Tinkerforge/wifi-v2-extension/software/src/configuration.c

/* WIFI Extension 2.0
 * Copyright (C) 2015 Olaf Lüke <olaf@tinkerforge.com>
 * Copyright (C) 2016 Ishraq Ibne Ashraf <ishraq@tinkerforge.com>
 * Copyright (C) 2020 Matthias Bolte <matthias@tinkerforge.com>
 *
 * configuration.c: WIFI Extension configuration handling
 *
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
 * You should have received a copy of the GNU Lesser General Public
 * License along with this library; if not, write to the
 * Free Software Foundation, Inc., 59 Temple Place - Suite 330,
 * Boston, MA 02111-1307, USA.
 */

#define _GNU_SOURCE // for strnlen
#undef __STRICT_ANSI__ // for strnlen

#include <string.h> // for strnlen

#include "configuration.h"
#include "espmissingincludes.h"
#include "eeprom.h"
#include "ip_addr.h"
#include "espconn.h"
#include "osapi.h"
#include "user_interface.h"
#include "pearson_hash.h"
#include "communication.h"
#include "logging.h"
#include "mesh.h"
#include "tfp_mesh_connection.h"
#include "tfp_connection.h"

extern os_timer_t tmr_tfp_mesh_enable;

const Configuration configuration_default = {
	// Configuration info
	.conf_checksum = 0,
	.conf_version = CONFIGURATION_EXPECTED_VERSION,
	.conf_length = sizeof(Configuration),

	// General configuration
	.general_port = 4223,
	.general_websocket_port = 4280,
	.general_website_port = 80,
	.general_phy_mode = 1,
	.general_sleep_mode = 0, // Currently unused
	.general_website = 1,
	.general_authentication_secret = "",

	// Client configuration
	.client_enable = 1,
	.client_ssid = "Your Access Point",
	.client_ip = {0, 0, 0, 0},
	.client_subnet_mask = {0, 0, 0, 0},
	.client_gateway = {0, 0, 0, 0},
	.client_mac_address = {0, 0, 0, 0, 0, 0},
	.client_bssid = {0, 0, 0, 0, 0, 0},
	.client_hostname = "wifi-extension-v2",
	.client_password = "password",

	// AP configuration
	.ap_enable = 1,
	.ap_ssid = "WIFI Extension 2.0 Access Point",
	.ap_ip = {0, 0, 0, 0},
	.ap_subnet_mask = {0, 0, 0, 0},
	.ap_gateway = {0, 0, 0, 0},
	.ap_encryption = 4,
	.ap_hidden = false,
	.ap_mac_address = {0, 0, 0, 0, 0, 0},
	.ap_channel = 1,
	.ap_hostname = "\0", // Currently unused
	.ap_password = "password",

	// Mesh configuration
	.mesh_enable = 0,
	.mesh_router_ssid = "Your Access Point",
	.mesh_router_password = "password",
	.mesh_root_ip = {0, 0, 0, 0},
	.mesh_root_subnet_mask = {0, 0, 0, 0},
	.mesh_root_gateway = {0, 0, 0, 0},
	.mesh_router_bssid = {0, 0, 0, 0, 0, 0}, // Must be set if mesh router is hidden.
	.mesh_group_ssid_prefix = "TF_MESH",
	.mesh_password = "password",
	.mesh_group_id = {0x1A, 0xFE, 0x34, 0x00, 0x00, 0x00},
	.mesh_gateway_hostname = "\0", // Currently unused.
	.mesh_gateway_ip = {0, 0, 0, 0}, // IP of the brickd to connect the mesh network to.
	.mesh_gateway_port = 4240, // Port of the brickd to connect the mesh network to.
};

Configuration configuration_current;
Configuration configuration_current_to_save;

uint8_t ICACHE_FLASH_ATTR configuration_calculate_checksum(void *configuration) {
	uint8_t checksum = 0;

	uint8_t *conf_array = (uint8_t *)configuration;
	for(uint16_t i = 1; i < sizeof(Configuration); i++) {
		PEARSON(checksum, conf_array[i]);
	}

	return checksum;
}

bool ICACHE_FLASH_ATTR configuration_check_checksum(void) {
	const uint8_t checksum = configuration_calculate_checksum(&configuration_current);
	return checksum == configuration_current.conf_checksum;
}

void ICACHE_FLASH_ATTR configuration_use_default(void) {
	os_memcpy(&configuration_current, &configuration_default, sizeof(Configuration));
}

void ICACHE_FLASH_ATTR configuration_load_from_eeprom(void) {
	for(uint8_t i = 0; i < 3; ++i) {
		if(eeprom_read(CONFIGURATION_ADDRESS, (uint8_t*)&configuration_current, sizeof(Configuration)) &&
		   configuration_current.conf_version == CONFIGURATION_EXPECTED_VERSION &&
		   configuration_check_checksum()) {
			return; // Success
		}
	}

	// In case of any kind of error we use the default configuration
	// but don't save it to the EEPROM for the next restart.
	configuration_use_default();
}

uint8_t ICACHE_FLASH_ATTR configuration_save_to_eeprom(void) {
	configuration_current_to_save.conf_checksum = configuration_calculate_checksum(&configuration_current_to_save);
	if(eeprom_write(CONFIGURATION_ADDRESS, (uint8_t*)&configuration_current_to_save, sizeof(Configuration))) {
		return 0;
	}

	return 1;
}

bool ICACHE_FLASH_ATTR configuration_check_array_null(const uint8_t *array, const uint8_t length) {
	for(uint8_t i = 0; i < length; i++) {
		if(array[i] != 0) {
			return false;
		}
	}

	return true;
}

void ICACHE_FLASH_ATTR configuration_apply_client(void) {
	struct station_config conf;
	os_memcpy(conf.ssid, configuration_current.client_ssid, CONFIGURATION_SSID_MAX_LENGTH);
	os_memcpy(conf.password, configuration_current.client_password, CONFIGURATION_PASSWORD_MAX_LENGTH);
	os_memcpy(conf.bssid, configuration_current.client_bssid, 6);
	if(configuration_check_array_null(configuration_current.client_bssid, 6)) {
		conf.bssid_set = 0;
	}
	else{
		conf.bssid_set = 1;
	}
	wifi_station_set_config_current(&conf);

	if(configuration_check_array_null(configuration_current.client_ip, 4)) {
		wifi_station_dhcpc_start();
	} else {
		wifi_station_dhcpc_stop();
		struct ip_info info;
		IP4_ADDR(&info.ip, configuration_current.client_ip[0],
		                   configuration_current.client_ip[1],
		                   configuration_current.client_ip[2],
		                   configuration_current.client_ip[3]);
		IP4_ADDR(&info.gw, configuration_current.client_gateway[0],
		                   configuration_current.client_gateway[1],
		                   configuration_current.client_gateway[2],
		                   configuration_current.client_gateway[3]);
		IP4_ADDR(&info.netmask, configuration_current.client_subnet_mask[0],
		                        configuration_current.client_subnet_mask[1],
		                        configuration_current.client_subnet_mask[2],
		                        configuration_current.client_subnet_mask[3]);
		wifi_set_ip_info(STATION_IF, &info);
	}

	if(!configuration_check_array_null(configuration_current.client_mac_address, 6)) {
		wifi_set_macaddr(STATION_IF, configuration_current.client_mac_address);
	}

	char client_hostname[CONFIGURATION_HOSTNAME_MAX_LENGTH + 1] = {0}; // +1 for NUL-terminator
	os_memcpy(client_hostname, configuration_current.client_hostname, CONFIGURATION_HOSTNAME_MAX_LENGTH);

	wifi_station_set_hostname(client_hostname);
	wifi_station_set_reconnect_policy(true); // Always call from user_init
}

void ICACHE_FLASH_ATTR configuration_apply_ap(void) {
	struct softap_config conf;
	os_memcpy(conf.ssid, configuration_current.ap_ssid, CONFIGURATION_SSID_MAX_LENGTH);
	os_memcpy(conf.password, configuration_current.ap_password, CONFIGURATION_PASSWORD_MAX_LENGTH);
	conf.ssid_len = strnlen(configuration_current.ap_ssid, CONFIGURATION_SSID_MAX_LENGTH);
	conf.channel = configuration_current.ap_channel;

	if(configuration_current.ap_encryption == 1){
		// WEP is not supported. Switches to default WPA/WPA2.
		conf.authmode = 4;
		configuration_current.ap_encryption = 4;
	}
	else{
		conf.authmode = configuration_current.ap_encryption;
	}

	conf.ssid_hidden = configuration_current.ap_hidden;
	conf.max_connection = 4; // Max number here is 4
	conf.beacon_interval = 100;
	wifi_softap_set_config_current(&conf);

	if(configuration_check_array_null(configuration_current.ap_ip, 4)) {
		wifi_softap_dhcps_stop();
		struct ip_info info;
		IP4_ADDR(&info.ip, 192, 168, 42, 1);
		IP4_ADDR(&info.gw, 192, 168, 42, 1);
		IP4_ADDR(&info.netmask, 255, 255, 255, 0);
		wifi_set_ip_info(SOFTAP_IF, &info);

		struct dhcps_lease dhcp_lease;
		IP4_ADDR(&dhcp_lease.start_ip, 192, 168, 42, 100);
		IP4_ADDR(&dhcp_lease.end_ip, 192, 168, 42, 105);
		wifi_softap_set_dhcps_lease(&dhcp_lease);

		uint8 mode = 1;
		wifi_softap_set_dhcps_offer_option(OFFER_ROUTER, &mode);

		wifi_softap_dhcps_start();
	} else {
		wifi_softap_dhcps_stop();
		struct ip_info info;
		IP4_ADDR(&info.ip, configuration_current.ap_ip[0],
		                   configuration_current.ap_ip[1],
		                   configuration_current.ap_ip[2],
		                   configuration_current.ap_ip[3]);
		IP4_ADDR(&info.gw, configuration_current.ap_gateway[0],
		                   configuration_current.ap_gateway[1],
		                   configuration_current.ap_gateway[2],
		                   configuration_current.ap_gateway[3]);
		IP4_ADDR(&info.netmask, configuration_current.ap_subnet_mask[0],
		                        configuration_current.ap_subnet_mask[1],
		                        configuration_current.ap_subnet_mask[2],
		                        configuration_current.ap_subnet_mask[3]);
		wifi_set_ip_info(SOFTAP_IF, &info);
	}

	if(!configuration_check_array_null(configuration_current.ap_mac_address, 6)) {
		wifi_set_macaddr(SOFTAP_IF, configuration_current.ap_mac_address);
	}

	/* TODO: MDNS does not seem to work currently.
	 *       Check again in later SDK version
		struct mdns_info dns;
		struct ip_info sta_ip;
		wifi_get_ip_info(STATION_IF, &sta_ip);
		char host_name[] = "host";
		char server_name[] = "server";
		dns.host_name = (char*)&host_name;
		dns.server_name = (char*)&server_name;
		dns.txt_data[0] = (char*)NULL;
		dns.ipAddr = sta_ip.ip.addr;
		dns.server_port = 80;
		espconn_mdns_init(&dns);
	*/
}

void ICACHE_FLASH_ATTR configuration_apply_tf_mesh(void) {
	char hostname[32];
	bool setup_ok = true;
	uint8_t mac_sta_if[6];
	struct station_config config_st;
	struct softap_config config_ap;
	struct ip_info ip_static_mesh_root;
	char mesh_group_ssid_prefix_str[sizeof(configuration_current.mesh_group_ssid_prefix) + 1];

	logi("MSH:Applying mesh configuration\n");

	/*
	 * For mesh, STATION+AP mode is required.
	 *
	 * The APIs used to configure station interface requires proper mode be enabled
	 * before using them.
	 */
	if(!wifi_set_opmode(STATIONAP_MODE)) {
		setup_ok = false;

		loge("MSH:Setting STATION+AP mode failed\n");
	}

	/*
	 * Mesh requires the softap configuration to be cleared so the mesh library
	 * can configure the softap accordingly.
	 */
	os_bzero(&config_ap, sizeof(config_ap));

	wifi_softap_set_config_current(&config_ap);

	os_bzero(&config_st, sizeof(config_st));

	/*
	 * FIXME: Because of a bug in the mesh library the mesh router SSID must be
	 * NULL terminated, effectively making maximum 31 characters long mesh router
	 * SSID.
	 */
	configuration_current.mesh_router_ssid[CONFIGURATION_SSID_MAX_LENGTH - 1] = '\0';

	os_memcpy(config_st.ssid, configuration_current.mesh_router_ssid,
		sizeof(configuration_current.mesh_router_ssid));

	os_bzero(&config_st.bssid, sizeof(config_st.bssid));

	if(configuration_check_array_null(configuration_current.mesh_router_bssid,
		sizeof(configuration_current.mesh_router_bssid))) {
			config_st.bssid_set = 0;
	}
	else {
		config_st.bssid_set = 1;
		os_memcpy(&config_st.bssid, configuration_current.mesh_router_bssid,
		sizeof(configuration_current.mesh_router_bssid));
	}

	os_memcpy(config_st.password, configuration_current.mesh_router_password,
		sizeof(configuration_current.mesh_router_password));

	// Set hostname.
	os_bzero(&mac_sta_if, sizeof(mac_sta_if));

	if(!wifi_get_macaddr(STATION_IF, mac_sta_if)) {
		setup_ok = false;

		loge("MSH:Getting station MAC failed\n");
	}
	else {
		os_bzero(&mesh_group_ssid_prefix_str, sizeof(mesh_group_ssid_prefix_str));
		os_memcpy(&mesh_group_ssid_prefix_str,
							configuration_current.mesh_group_ssid_prefix,
							sizeof(configuration_current.mesh_group_ssid_prefix));

		os_bzero(&hostname, sizeof(hostname));

		os_sprintf(hostname,
							 FMT_MESH_STATION_HOSTNAME,
							 mesh_group_ssid_prefix_str,
							 mac_sta_if[3],
							 mac_sta_if[4],
							 mac_sta_if[5]);

		if(!wifi_station_set_hostname(hostname)) {
			setup_ok = false;

			loge("MSH:Setting hostname failed\n");
		}
		else {
			logi("MSH:Station hostname = %s\n", hostname);
		}
	}

	// Static IP configuration for mesh router.
	if(!configuration_check_array_null(configuration_current.mesh_root_ip,
		sizeof(configuration_current.mesh_root_ip))) {
			wifi_station_dhcpc_stop();

			os_bzero(&ip_static_mesh_root, sizeof(ip_static_mesh_root));

			IP4_ADDR(&ip_static_mesh_root.ip,
				configuration_current.mesh_root_ip[0],
				configuration_current.mesh_root_ip[1],
				configuration_current.mesh_root_ip[2],
				configuration_current.mesh_root_ip[3]);

			IP4_ADDR(&ip_static_mesh_root.netmask,
				configuration_current.mesh_root_subnet_mask[0],
				configuration_current.mesh_root_subnet_mask[1],
				configuration_current.mesh_root_subnet_mask[2],
				configuration_current.mesh_root_subnet_mask[3]);

			IP4_ADDR(&ip_static_mesh_root.gw,
				configuration_current.mesh_root_gateway[0],
				configuration_current.mesh_root_gateway[1],
				configuration_current.mesh_root_gateway[2],
				configuration_current.mesh_root_gateway[3]);

			wifi_set_ip_info(STATION_IF, &ip_static_mesh_root);
	}
	else {
		wifi_station_dhcpc_start();
	}

	// Setup mesh network parameters.
	if(!espconn_mesh_set_router(&config_st)) {
		setup_ok = false;

		loge("MSH:Set router failed\n");
	}

	os_bzero(&mesh_group_ssid_prefix_str, sizeof(mesh_group_ssid_prefix_str));
	os_memcpy(&mesh_group_ssid_prefix_str,
						configuration_current.mesh_group_ssid_prefix,
						sizeof(configuration_current.mesh_group_ssid_prefix));

	if(!espconn_mesh_set_ssid_prefix(mesh_group_ssid_prefix_str,
		os_strlen(mesh_group_ssid_prefix_str))) {
			setup_ok = false;

			loge("MSH:Set SSID prefix failed\n");
	}

	if(!espconn_mesh_group_id_init((uint8_t *)configuration_current.mesh_group_id,
	sizeof(configuration_current.mesh_group_id))) {
		setup_ok = false;

		loge("MSH:Set group ID failed\n");
	}

	/*
	 * Even though we call espconn_mesh_connect() in tfp_mesh_open_connection()
	 * with configured mesh gateway IP and socket, espconn_mesh_server_init() must
	 * be still be called here.
	 */
	if(!espconn_mesh_server_init((struct ip_addr *)configuration_current.mesh_gateway_ip,
	configuration_current.mesh_gateway_port)) {
		setup_ok = false;

		loge("MSH:Mesh server init failed\n");
	}

	/*
	 * Currently intra-mesh node comunication is encrypted with WPA/WPA2
	 * by default with password 1234567890 which is transparent to the user.
	 */
	if(!espconn_mesh_encrypt_init(AUTH_WPA_WPA2_PSK, configuration_current.mesh_password,
		os_strlen(configuration_current.mesh_password))) {
			setup_ok = false;

			loge("MSH:Encrypt init failed\n");
	}

	// Callback for the event when a new child joins a node.
	if(!espconn_mesh_regist_usr_cb(cb_tfp_mesh_new_node)) {
		setup_ok = false;

		loge("MSH:CB register new child failed\n");
	}

	if(!setup_ok) {
		loge("MSH:Configuring mesh parameters failed\n");

		return;
	}
	else {
		logi("MSH:Configuring mesh parameters OK\n");
	}

	espconn_mesh_print_ver();

	#ifdef MESH_SINGLE_ROOT_NODE
		#if(MESH_SINGLE_ROOT_NODE)
			unsigned char random_number = 0;

			do {
				if(os_get_random((unsigned char *)&random_number, 1) != 0) {
					loge("MSH:Failed to get random duration to enable mesh\n");

					return;
				}
			}
			while(random_number > TIME_RANDOM_WAIT_MAX ||
						random_number < TIME_RANDOM_WAIT_MIN);

			logi("MSH:Enabling in %d seconds\n", random_number);

			tfp_mesh_disarm_all_timers();

			tfp_mesh_arm_timer(&tmr_tfp_mesh_enable,
												 random_number * 1000,
												 false,
												 cb_tmr_tfp_mesh_enable,
												 NULL);

			return;
		#endif
	#endif

	/*
	 * Enable mesh (drum roll...)
	 *
	 * This function must be called from within user_init() function.
	 */
	espconn_mesh_enable(cb_tfp_mesh_enable, MESH_ONLINE);
}

void ICACHE_FLASH_ATTR configuration_apply_during_init(void) {
	// TODO: Currently not implemented in brickv
	wifi_set_sleep_type(NONE_SLEEP_T);

	if(configuration_current.mesh_enable) {
		configuration_apply_tf_mesh();

		return;
	}
	else if(configuration_current.client_enable && configuration_current.ap_enable) {
		wifi_set_opmode_current(STATIONAP_MODE);
	}
	else if(configuration_current.client_enable) {
		wifi_set_opmode_current(STATION_MODE);
	}
	else if(configuration_current.ap_enable) {
		wifi_set_opmode_current(SOFTAP_MODE);
	}
	else {
		wifi_set_opmode_current(NULL_MODE);
	}

	wifi_set_phy_mode(configuration_current.general_phy_mode+1);

	// Client
	if(configuration_current.client_enable) {
		configuration_apply_client();
	}

	// Access Point
	if(configuration_current.ap_enable) {
		configuration_apply_ap();
	}

	// Do always call during user_init, otherwise it will only be effective after restart!
	wifi_station_set_auto_connect(1);
}

void ICACHE_FLASH_ATTR configuration_apply_post_init(void) {
	/*
	 * Station connect can only be called after user_init.
	 *
	 * No need to explicitly connect station when in mesh mode as it is handled
	 * by the mesh library.
	 */
	if(!configuration_current.mesh_enable) {
		wifi_station_connect();
	}
}
