Tinkerforge/wifi-v2-extension/software/src/tfp_connection.c

/* WIFI Extension 2.0
 * Copyright (C) 2015 Olaf Lüke <olaf@tinkerforge.com>
 * Copyright (C) 2016 Ishraq Ibne Ashraf <ishraq@tinkerforge.com>
 *
 * tfp_connection.c: Implementation of connection for Tinkerforge protocol
 *
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
 * You should have received a copy of the GNU Lesser General Public
 * License along with this library; if not, write to the
 * Free Software Foundation, Inc., 59 Temple Place - Suite 330,
 * Boston, MA 02111-1307, USA.
 */

#include "tfp_connection.h"
#include "gpio.h"
#include "espmissingincludes.h"
#include "osapi.h"
#include "ip_addr.h"
#include "espconn.h"
#include "uart_connection.h"
#include "brickd.h"
#include "ringbuffer.h"
#include "communication.h"
#include "configuration.h"
#include "user_interface.h"
#include "logging.h"
#include "tfp_mesh_connection.h"

extern GetWifi2StatusReturn gw2sr;
extern Configuration configuration_current;

Ringbuffer tfp_rb;
bool tfp_is_hold = false;
uint8_t tfp_rb_buffer[TFP_RING_BUFFER_SIZE];
TFPConnection tfp_cons[TFP_MAX_CONNECTIONS];

void ICACHE_FLASH_ATTR tfp_init_con(const int8_t cid) {
	tfp_cons[cid].recv_buffer_index = 0;
	tfp_cons[cid].recv_buffer_expected_length = TFP_MIN_LENGTH;
	tfp_cons[cid].state = TFP_CON_STATE_CLOSED;
	tfp_cons[cid].cid   = cid;
	tfp_cons[cid].con   = NULL;
	tfp_cons[cid].websocket_state = WEBSOCKET_STATE_NO_WEBSOCKET;
	tfp_cons[cid].send_buffer_length = 0;

	if(configuration_current.general_authentication_secret[0] != '\0') {
		tfp_cons[cid].brickd_authentication_state = BRICKD_AUTHENTICATION_STATE_ENABLED;
	}
	else {
		tfp_cons[cid].brickd_authentication_state = BRICKD_AUTHENTICATION_STATE_DISABLED;
	}
}

void ICACHE_FLASH_ATTR tfp_write_finish_callback(void *arg) {
	struct espconn *con = (struct espconn *)arg;
	TFPConnection *tfp_con = (TFPConnection *)con->reverse;

	packet_counter(con, PACKET_COUNT_TX);

	if(tfp_con->state == TFP_CON_STATE_CLOSED_AFTER_SEND) {
		espconn_disconnect(tfp_con->con);
	}
	else {
		tfp_con->state = TFP_CON_STATE_OPEN;
	}
}

void ICACHE_FLASH_ATTR tfp_handle_packet(const uint8_t *data, const uint8_t length) {
	// If ringbuffer not empty we add data to ringbuffer (we want to keep order)
	// Else if we can't immediately send to master brick we also add to ringbuffer
	if(!ringbuffer_is_empty(&tfp_rb) || uart_con_send(data, length) == 0) {
		if(ringbuffer_get_free(&tfp_rb) > (length + 2)) {
			for(uint8_t i = 0; i < length; i++) {
				if(!ringbuffer_add(&tfp_rb, data[i])) {
					// Should be unreachable
					loge("Ringbuffer full!\n");
				}
			}
		} else {
			logw("Message does not fit in Buffer: %d < %d\n", ringbuffer_get_free(&tfp_rb), length + 2);
		}
	}
}

void ICACHE_FLASH_ATTR tfp_recv_hold(void) {
	if(!tfp_is_hold) {
		for(uint8_t i = 0; i < TFP_MAX_CONNECTIONS; i++) {
			if(tfp_cons[i].state == TFP_CON_STATE_OPEN || tfp_cons[i].state == TFP_CON_STATE_SENDING) {
				espconn_recv_hold(tfp_cons[i].con);
			}
		}

		logd("hold: %d\n", ringbuffer_get_free(&tfp_rb));
		tfp_is_hold = true;
	}
}

void ICACHE_FLASH_ATTR tfp_recv_unhold(void) {
	if(tfp_is_hold) {
		for(uint8_t i = 0; i < TFP_MAX_CONNECTIONS; i++) {
			if(tfp_cons[i].state == TFP_CON_STATE_OPEN || tfp_cons[i].state == TFP_CON_STATE_SENDING) {
				espconn_recv_unhold(tfp_cons[i].con);
			}
		}

		logd("unhold: %d\n", ringbuffer_get_free(&tfp_rb));
		tfp_is_hold = false;
	}
}

void ICACHE_FLASH_ATTR tfp_recv_callback(void *arg, char *pdata, unsigned short len) {
	struct espconn *con = (struct espconn *)arg;
	TFPConnection *tfp_con = (TFPConnection *)con->reverse;

	packet_counter(con, PACKET_COUNT_RX);

	for(uint32_t i = 0; i < len; i++) {
		tfp_con->recv_buffer[tfp_con->recv_buffer_index] = pdata[i];
		if(tfp_con->recv_buffer_index == TFP_RECV_INDEX_LENGTH) {
			const uint8_t length = tfp_con->recv_buffer[TFP_RECV_INDEX_LENGTH];
			if(length < TFP_MIN_LENGTH || length > TFP_MAX_LENGTH) {
				logi("Received malformed packet with length %d\n\r", tfp_con->recv_buffer_index);
				tfp_con->recv_buffer_index = 0;
				tfp_con->recv_buffer_expected_length = TFP_MIN_LENGTH;
				espconn_disconnect(con);
				return;
			}
			tfp_con->recv_buffer_expected_length = length;
		}

		tfp_con->recv_buffer_index++;
		if(tfp_con->recv_buffer_index == tfp_con->recv_buffer_expected_length) {
			if(!com_handle_message(tfp_con->recv_buffer,
			                       tfp_con->recv_buffer_expected_length,
			                       tfp_con->cid)) {
				brickd_route_from(tfp_con->recv_buffer, tfp_con->cid);
				tfp_handle_packet(tfp_con->recv_buffer,
				                  tfp_con->recv_buffer_expected_length);
			}

			tfp_con->recv_buffer_index = 0;
			tfp_con->recv_buffer_expected_length = TFP_MIN_LENGTH;
		}
	}

	if(ringbuffer_get_free(&tfp_rb) < (5*MTU_LENGTH + 2)) {
		tfp_recv_hold();
	}
}

void ICACHE_FLASH_ATTR tfp_disconnect_callback(void *arg) {
	struct espconn *con = (struct espconn *)arg;
	TFPConnection *tfp_con = (TFPConnection *)con->reverse;

	tfp_init_con(tfp_con->cid);

	logd("tfp_disconnect_callback: cid %d\n", tfp_con->cid);
}

// This is called if an error is detected, it does not reconnect...
void ICACHE_FLASH_ATTR tfp_reconnect_callback(void *arg, sint8 error) {
	struct espconn *con = (struct espconn *)arg;
	TFPConnection *tfp_con = (TFPConnection *)con->reverse;

	tfp_init_con(tfp_con->cid);

	logd("tfp_reconnect_callback: cid %d -> %d\n", tfp_con->cid, error);
}

void ICACHE_FLASH_ATTR tfp_connect_callback(void *arg) {
	uint8_t i = 0;

	for(; i < TFP_MAX_CONNECTIONS; i++) {
		if(tfp_cons[i].state == TFP_CON_STATE_CLOSED) {
			// If there are any remaining routes in brickd routing table, remove them now
			brickd_disconnect(i);
			tfp_cons[i].con = arg;
			tfp_cons[i].con->reverse = &tfp_cons[i];
			tfp_cons[i].state = TFP_CON_STATE_OPEN;
			tfp_cons[i].send_buffer_length = 0;
			logd("tfp_connect_callback: cid %d\n", tfp_cons[i].cid);
			break;
		}
	}

	if(i == TFP_MAX_CONNECTIONS) {
		logw("Too many open connections, can't handle more\n");
		/*
		 * TODO: according to the documentation we can not call espconn_disconnect
		 * in callback.
		 */

		// espconn_disconnect(arg);
		return;
	}

	espconn_set_opt(arg, ESPCONN_NODELAY);
	espconn_set_opt(arg, ESPCONN_COPY);

	espconn_regist_recvcb((struct espconn *)arg, tfp_recv_callback);
	espconn_regist_disconcb((struct espconn *)arg, tfp_disconnect_callback);
	espconn_regist_write_finish((struct espconn *)arg, tfp_write_finish_callback);
	espconn_regist_sentcb((struct espconn *)arg, tfp_write_finish_callback);
}

static bool ICACHE_FLASH_ATTR tfp_send_check_buffer(const int8_t cid) {
	if(cid == -1) { // Broadcast
		for(uint8_t i = 0; i < TFP_MAX_CONNECTIONS; i++) {
			if(tfp_cons[i].state == TFP_CON_STATE_SENDING || tfp_cons[i].send_buffer_length != 0) {
				// If we need to broadcast and one of the recipients has a full
				// buffer, we have to return false
				return false;
			}
		}
	} else {
		if(tfp_cons[cid].state == TFP_CON_STATE_SENDING || tfp_cons[cid].send_buffer_length != 0) {
			return false;
		}
	}

	return true;
}

bool ICACHE_FLASH_ATTR tfp_send_w_cid(const uint8_t *data,
                                      const uint8_t length,
                                      const uint8_t cid) {
	if(!configuration_current.mesh_enable) {
		/*
		 * FIXME: Shouldn't the buffering mechanism used for sending mesh mode packets
		 * also be used for non-mesh send? As it is documented that packets should be
		 * sent from the sent callback of the previous packet.
		 */
		if(tfp_cons[cid].state == TFP_CON_STATE_OPEN) {
			tfp_cons[cid].state = TFP_CON_STATE_SENDING;
			tfp_cons[cid].send_buffer_length = length;
			os_memcpy(tfp_cons[cid].send_buffer, data, length);
			int8_t ret = espconn_send(tfp_cons[cid].con, tfp_cons[cid].send_buffer, length);
			if(ret == ESPCONN_OK) {
				tfp_cons[cid].send_buffer_length = 0;
			} else {
				tfp_cons[cid].state = TFP_CON_STATE_OPEN;
			}

			return true;
		}

		// If the connection has been closed by now we throw the packet away
		if(tfp_cons[cid].state == TFP_CON_STATE_CLOSED) {
			return true;
		}

		return false;
	}
	else {
		tfp_mesh_send_handler(data, length);

		return true;
	}
}

bool ICACHE_FLASH_ATTR tfp_send(const uint8_t *data, const uint8_t length) {
	// cid == -2 => send back via UART
	if(com_handle_message(data, length, -2)) {
		return true;
	}

	// We only peak at the routing table here (and delete the route manually if
	// we can fit the data in our buffer). It would be very expensive to first
	// peak and then discover the route again.
	BrickdRouting *match = NULL;
	int8_t cid = brickd_route_to_peak(data, &match);

	if(!brickd_check_auth((const MessageHeader*)data, cid)) {
		brickd_remove_route(match);
		return true;
	}

	// Add websocket header if necessary
	uint8_t data_with_websocket_header[TFP_SEND_BUFFER_SIZE + sizeof(WebsocketFrameClientToServer)];
	int16_t length_with_websocket_header = tfpw_insert_websocket_header(cid, data_with_websocket_header, data, length);

	// -1 = We use websocket but state is not OK for sending
	if(length_with_websocket_header == -1) {
		return false;
	}

	if (!configuration_current.mesh_enable) {
		/*
		 * First let's check if everything fits in the buffers. This is only done if
		 * mesh isn't enabled. When mesh is enabled, dedicated buffer is used for
		 * sending.
		 */
		if(!tfp_send_check_buffer(cid)) {
			return false;
		}

		// Remove match from brickd routing table only if we now that we can fit
		// the data in the buffer
		brickd_remove_route(match);

		// Broadcast.
		if(cid == -1) {
			/*
			 * Broadcast is handled differently when mesh is enabled as then there is
			 * only one socket connection involved.
			 */
			for(uint8_t i = 0; i < TFP_MAX_CONNECTIONS; i++) {
				if(tfp_cons[i].state == TFP_CON_STATE_OPEN) {
					tfp_cons[i].state = TFP_CON_STATE_SENDING;
					tfp_cons[i].send_buffer_length = length;
					if(tfp_cons[i].websocket_state == WEBSOCKET_STATE_NO_WEBSOCKET) {
						os_memcpy(tfp_cons[i].send_buffer, data, length);
					}
					else {
						os_memcpy(tfp_cons[i].send_buffer, data_with_websocket_header, length_with_websocket_header);
						tfp_cons[i].send_buffer_length = length_with_websocket_header;
					}

					int ret = -42;
					if(system_get_free_heap_size() > TFP_MIN_ESP_HEAP_SIZE) {
						ret = espconn_send(tfp_cons[i].con, tfp_cons[i].send_buffer, tfp_cons[i].send_buffer_length);
					}
					if(ret == ESPCONN_OK) {
						tfp_cons[i].send_buffer_length = 0;
					} else {
						tfp_cons[i].state = TFP_CON_STATE_OPEN;
					}
				}
			}
		}
		// Unicast.
		else {
			// If the socket has been closed by now, we just ignore the packet.
			if(tfp_cons[cid].state == TFP_CON_STATE_OPEN) {
				tfp_cons[cid].send_buffer_length =  length;
				tfp_cons[cid].state = TFP_CON_STATE_SENDING;

				if(tfp_cons[cid].websocket_state == WEBSOCKET_STATE_NO_WEBSOCKET) {
					os_memcpy(tfp_cons[cid].send_buffer, data, length);
				} else {
					os_memcpy(tfp_cons[cid].send_buffer, data_with_websocket_header, length_with_websocket_header);
					tfp_cons[cid].send_buffer_length = length_with_websocket_header;
				}

				int ret = -42;
				if(system_get_free_heap_size() > TFP_MIN_ESP_HEAP_SIZE) {
					ret = espconn_send(tfp_cons[cid].con, tfp_cons[cid].send_buffer, tfp_cons[cid].send_buffer_length);
				}
				if(ret == ESPCONN_OK) {
					tfp_cons[cid].send_buffer_length = 0;
				} else {
					tfp_cons[cid].state = TFP_CON_STATE_OPEN;
				}
			}
		}

		if(ringbuffer_get_free(&tfp_rb) > (6*MTU_LENGTH + 2)) {
			tfp_recv_unhold();
		}

		return true;
	}
	else {
		// Remove match from brickd routing table
		brickd_remove_route(match);

		tfp_mesh_send_handler(data, length);

		return true;
	}
}

// TODO: Does this have to be available after espconn_regist_time call?
//       I.e. can we just have it locally in the function?
static struct espconn tfp_con_listen;
static esp_tcp tfp_con_listen_tcp;

void ICACHE_FLASH_ATTR tfp_open_connection(void) {
	for(uint8_t i = 0; i < TFP_MAX_CONNECTIONS; i++) {
		tfp_init_con(i);
	}

	ets_memset(&tfp_con_listen, 0, sizeof(struct espconn));

	// Initialize the ESPConn
	espconn_create(&tfp_con_listen);
	tfp_con_listen.type = ESPCONN_TCP;
	tfp_con_listen.state = ESPCONN_NONE;

	// Make it a TCP connection
	tfp_con_listen.proto.tcp = &tfp_con_listen_tcp;
	tfp_con_listen.proto.tcp->local_port = configuration_current.general_port;

	espconn_regist_reconcb(&tfp_con_listen, tfp_reconnect_callback);
	espconn_regist_connectcb(&tfp_con_listen, tfp_connect_callback);

	// Start listening
	espconn_accept(&tfp_con_listen);

	// Set server timeout (in seconds)
	espconn_regist_time(&tfp_con_listen, 7200, 0);

}

// Check send buffer for unsent data
void ICACHE_FLASH_ATTR tfp_check_send_buffer(void) {
	for(uint8_t i = 0; i < TFP_MAX_CONNECTIONS; i++) {
		if(tfp_cons[i].state == TFP_CON_STATE_OPEN && tfp_cons[i].send_buffer_length != 0) {
			tfp_cons[i].state = TFP_CON_STATE_SENDING;

			int ret = -42;
			if(system_get_free_heap_size() > TFP_MIN_ESP_HEAP_SIZE) {
				ret = espconn_send(tfp_cons[i].con, tfp_cons[i].send_buffer, tfp_cons[i].send_buffer_length);
			}
			if(ret == ESPCONN_OK) {
				tfp_cons[i].send_buffer_length = 0;
			} else {
				tfp_cons[i].state = TFP_CON_STATE_OPEN;
			}
		}
	}
}

void ICACHE_FLASH_ATTR tfp_poll(void) {
	if(ringbuffer_is_empty(&tfp_rb)) {
		return;
	}

	uint8_t data[TFP_RECV_BUFFER_SIZE];
	uint8_t length = ringbuffer_peak(&tfp_rb, data, TFP_RECV_BUFFER_SIZE);

	if(length > TFP_RECV_BUFFER_SIZE) {
		ringbuffer_init(&tfp_rb, tfp_rb.buffer, tfp_rb.buffer_length);
		logd("tfp_poll: length > %d: %d\n", TFP_RECV_BUFFER_SIZE, length);
		return;
	}

	if(length < TFP_MIN_LENGTH) {
		ringbuffer_init(&tfp_rb, tfp_rb.buffer, tfp_rb.buffer_length);
		logd("tfp_poll: length < TFP_MIN_LENGTH\n");
		return;
	}

	if(uart_con_send(data, data[TFP_RECV_INDEX_LENGTH]) != 0) {
		ringbuffer_remove(&tfp_rb, data[TFP_RECV_INDEX_LENGTH]);
	} else {
		logd("tfp_poll send error\n");
	}
}

void ICACHE_FLASH_ATTR packet_counter(struct espconn *con, uint8_t direction) {
	uint8 ap_ip[4];
	uint8 ap_netmask[4];
	uint8 station_ip[4];
	uint8 station_netmask[4];
	uint8 connection_remote_ip[4];
	struct ip_info info_ap;
	struct ip_info info_station;

	switch(con->type) {
		case ESPCONN_TCP:
			connection_remote_ip[0] = con->proto.tcp->remote_ip[0];
			connection_remote_ip[1] = con->proto.tcp->remote_ip[1];
			connection_remote_ip[2] = con->proto.tcp->remote_ip[2];
			connection_remote_ip[3] = con->proto.tcp->remote_ip[3];
			break;

		case ESPCONN_UDP:
			connection_remote_ip[0] = con->proto.udp->remote_ip[0];
			connection_remote_ip[1] = con->proto.udp->remote_ip[1];
			connection_remote_ip[2] = con->proto.udp->remote_ip[2];
			connection_remote_ip[3] = con->proto.udp->remote_ip[3];
			break;

		default:
			return;
	}

	if(configuration_current.ap_enable) {
		wifi_get_ip_info(SOFTAP_IF, &info_ap);

		ap_ip[0] = ip4_addr1(&info_ap.ip);
		ap_ip[1] = ip4_addr2(&info_ap.ip);
		ap_ip[2] = ip4_addr3(&info_ap.ip);
		ap_ip[3] = ip4_addr4(&info_ap.ip);

		ap_netmask[0] = ip4_addr1(&info_ap.netmask);
		ap_netmask[1] = ip4_addr2(&info_ap.netmask);
		ap_netmask[2] = ip4_addr3(&info_ap.netmask);
		ap_netmask[3] = ip4_addr4(&info_ap.netmask);

		// Determine and match network address.
		if(((connection_remote_ip[0] & ap_netmask[0]) == \
			(ap_ip[0] & ap_netmask[0])) &&
		   ((connection_remote_ip[1] & ap_netmask[1]) == \
			(ap_ip[1] & ap_netmask[1])) &&
		   ((connection_remote_ip[2] & ap_netmask[2]) == \
			(ap_ip[2] & ap_netmask[2])) &&
		   ((connection_remote_ip[3] & ap_netmask[3]) == \
			(ap_ip[3] & ap_netmask[3]))) {
				if(direction == PACKET_COUNT_RX) {
					gw2sr.ap_rx_count++;
				} else if(direction == PACKET_COUNT_TX) {
					gw2sr.ap_tx_count++;
				}
		}
	}

	if(configuration_current.client_enable) {
		wifi_get_ip_info(STATION_IF, &info_station);

		station_ip[0] = ip4_addr1(&info_station.ip);
		station_ip[1] = ip4_addr2(&info_station.ip);
		station_ip[2] = ip4_addr3(&info_station.ip);
		station_ip[3] = ip4_addr4(&info_station.ip);

		station_netmask[0] = ip4_addr1(&info_station.netmask);
		station_netmask[1] = ip4_addr2(&info_station.netmask);
		station_netmask[2] = ip4_addr3(&info_station.netmask);
		station_netmask[3] = ip4_addr4(&info_station.netmask);

		// Determine and match network address.
		if(((connection_remote_ip[0] & station_netmask[0]) == \
			(station_ip[0] & station_netmask[0])) &&
		   ((connection_remote_ip[1] & station_netmask[1]) == \
			(station_ip[1] & station_netmask[1])) &&
		   ((connection_remote_ip[2] & station_netmask[2]) == \
			(station_ip[2] & station_netmask[2])) &&
		   ((connection_remote_ip[3] & station_netmask[3]) == \
			(station_ip[3] & station_netmask[3]))) {
				if(direction == PACKET_COUNT_RX) {
					gw2sr.client_rx_count++;
				} else if(direction == PACKET_COUNT_TX) {
					gw2sr.client_tx_count++;
				}
		}
	}
}
