Tinkerforge/wifi-v2-extension/software/src/tfp_mesh_connection.h

/* WIFI Extension 2.0
 * Copyright (C) 2016 Ishraq Ibne Ashraf <ishraq@tinkerforge.com>
 *
 * configuration.h: Mesh networking implementation
 *
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
 * You should have received a copy of the GNU Lesser General Public
 * License along with this library; if not, write to the
 * Free Software Foundation, Inc., 59 Temple Place - Suite 330,
 * Boston, MA 02111-1307, USA.
 */

#ifndef TFP_MESH_CONNECTION_H
#define TFP_MESH_CONNECTION_H

#include "tfp_connection.h"

#define TFP_MESH_MAX_LENGTH sizeof(struct mesh_header_format) + TFP_MAX_LENGTH + 1

#define FID_MASTER_RESET 243
#define FID_MASTER_STACK_ENUMERATE 252

/*
 * Applicable only when MESH_SINGLE_ROOT_NODE is enabled in config.h.
 *
 * In seconds.
 */
#define TIME_RANDOM_WAIT_MIN 2
#define TIME_RANDOM_WAIT_MAX 64
// In milliseconds.
#define TIME_HB_PING      8000
#define TIME_WAIT_OLLEH   8000
#define TIME_HB_WAIT_PONG (TIME_HB_PING/2)

#define TFP_MESH_MIN_LENGTH 16
#define TFP_MESH_HEADER_LENGTH_INDEX 3
// 64 full size (16+80+1=97 bytes) TFP mesh packets.
#define TFP_MESH_SEND_RING_BUFFER_SIZE 6208
#define FMT_MESH_STATION_HOSTNAME "%s_C_%X%X%X"

enum {
  MESH_PACKET_HELLO = 1,
  MESH_PACKET_OLLEH,
  MESH_PACKET_RESET,
  MESH_PACKET_HB_PING,
  MESH_PACKET_HB_PONG,
  MESH_PACKET_TFP
};

// TFP packet header.
typedef struct {
	uint32_t uid; // Always little-endian.
	uint8_t length;
	uint8_t function_id;
	uint8_t sequence_number_and_options;
	uint8_t error_code_and_future_use;
} __attribute__((packed)) tfp_packet_header_t;

// TFP packet with header.
typedef struct {
	tfp_packet_header_t header;
	uint8_t payload[64];
	uint8_t optional_data[8];
} __attribute__((packed)) tfp_packet_t;

// Mesh packet types.
typedef struct {
  struct mesh_header_format mesh_header;
  uint8_t type;
  bool is_root_node;
  uint8_t group_id[6];
  char prefix[16];
  uint8_t firmware_version[3];
} __attribute__((packed)) pkt_mesh_hello_t;

typedef struct {
	struct mesh_header_format header;
  uint8_t type;
} __attribute__((packed)) pkt_mesh_olleh_t;

typedef struct {
	struct mesh_header_format header;
  uint8_t type;
} __attribute__((packed)) pkt_mesh_reset_t;

typedef struct {
	struct mesh_header_format header;
  uint8_t type;
} __attribute__((packed)) pkt_mesh_hb_t;

typedef struct {
	struct mesh_header_format header;
  uint8_t type;
  tfp_packet_t pkt_tfp;
} __attribute__((packed)) pkt_mesh_tfp_t;

// Function prototypes.
void ICACHE_FLASH_ATTR init_tfp_con_mesh(void);
void ICACHE_FLASH_ATTR tfp_mesh_recv_hold(void);
void ICACHE_FLASH_ATTR tfp_mesh_recv_unhold(void);
void ICACHE_FLASH_ATTR tfp_mesh_open_connection(void);
void ICACHE_FLASH_ATTR tfp_mesh_pong_recv_handler(void);
void ICACHE_FLASH_ATTR tfp_mesh_send_buffer_clear(void);
void ICACHE_FLASH_ATTR tfp_mesh_disarm_all_timers(void);
bool ICACHE_FLASH_ATTR tfp_mesh_olleh_recv_handler(void);
void ICACHE_FLASH_ATTR tfp_mesh_arm_timer(os_timer_t *timer,
                                          uint32_t time_ms,
                                          bool repeat,
                                          os_timer_func_t *cb_func,
                                          void *arg_cb_func);
bool ICACHE_FLASH_ATTR tfp_mesh_send_buffer_check(uint8_t len);
bool ICACHE_FLASH_ATTR tfp_mesh_reset_recv_handler(void);
void ICACHE_FLASH_ATTR tfp_mesh_ping_recv_handler(pkt_mesh_hb_t *pkt_mesh_hb);
bool ICACHE_FLASH_ATTR tfp_mesh_tfp_recv_handler(pkt_mesh_tfp_t *tfp_mesh_pkt);
int8_t ICACHE_FLASH_ATTR tfp_mesh_send(void *arg, uint8_t *data, uint16_t length);
int8_t ICACHE_FLASH_ATTR tfp_mesh_send_handler(const uint8_t *data, uint8_t length);

// Callbacks.
void ICACHE_FLASH_ATTR cb_tfp_mesh_sent(void *arg);
void ICACHE_FLASH_ATTR cb_tfp_mesh_connect(void *arg);
void ICACHE_FLASH_ATTR cb_tfp_mesh_new_node(void *mac);
void ICACHE_FLASH_ATTR cb_tfp_mesh_disconnect(void *arg);
void ICACHE_FLASH_ATTR cb_tfp_mesh_enable(int8_t status);
void ICACHE_FLASH_ATTR cb_tfp_mesh_reconnect(void *arg, sint8 error);
void ICACHE_FLASH_ATTR cb_tfp_mesh_receive(void *arg, char *pdata, uint16_t len);

// Timer callbacks.
void cb_tmr_tfp_mesh_enable(void *arg);
void cb_tmr_tfp_mesh_hb_ping(void *arg);
void cb_tmr_tfp_mesh_wait_pong(void *arg);
void cb_tmr_tfp_mesh_wait_olleh(void *arg);

#endif
