Tinkerforge/wifi-v2-extension/software/src/logging.h

/* WIFI Extension 2.0
 * Copyright (C) 2015 Olaf Lüke <olaf@tinkerforge.com>
 *
 * logging.h: Simple logging functionality
 *
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
 * You should have received a copy of the GNU Lesser General Public
 * License along with this library; if not, write to the
 * Free Software Foundation, Inc., 59 Temple Place - Suite 330,
 * Boston, MA 02111-1307, USA.
 */

#ifndef LOGGING_H
#define LOGGING_H

#include "config.h"
#include "osapi.h"
#include "espmissingincludes.h"

#define LOGGING_DEBUG    0
#define LOGGING_INFO     1
#define LOGGING_WARNING  2
#define LOGGING_ERROR    3
#define LOGGING_FATAL    4
#define LOGGING_NONE     5

#ifndef LOGGING_LEVEL
#define LOGGING_LEVEL LOGGING_NONE
#endif

#if LOGGING_LEVEL < LOGGING_NONE
#define DEBUG_ENABLED
#endif


#if LOGGING_LEVEL <= LOGGING_DEBUG
#define logd(str,  ...) do{ os_printf("<D> " str, ##__VA_ARGS__); }while(0)
#define logwohd(str,  ...) do{ os_printf(str, ##__VA_ARGS__); }while(0)
#else
#define logd(str,  ...) {}
#define logwohd(str,  ...) {}
#endif

#if LOGGING_LEVEL <= LOGGING_INFO
#define logi(str,  ...) do{ os_printf("<I> " str, ##__VA_ARGS__); }while(0)
#define logwohi(str,  ...) do{ os_printf(str, ##__VA_ARGS__); }while(0)
#else
#define logi(str,  ...) {}
#define logwohi(str,  ...) {}
#endif

#if LOGGING_LEVEL <= LOGGING_WARNING
#define logw(str,  ...) do{ os_printf("<W> " str, ##__VA_ARGS__); }while(0)
#define logwohw(str,  ...) do{ os_printf(str, ##__VA_ARGS__); }while(0)
#else
#define logw(str,  ...) {}
#define logwohw(str,  ...) {}
#endif

#if LOGGING_LEVEL <= LOGGING_ERROR
#define loge(str,  ...) do{ os_printf("<E> " str, ##__VA_ARGS__); }while(0)
#define logwohe(str,  ...) do{ os_printf(str, ##__VA_ARGS__); }while(0)
#else
#define loge(str,  ...) {}
#define logwohe(str,  ...) {}
#endif

#if LOGGING_LEVEL <= LOGGING_FATAL
#define logf(str,  ...) do{ os_printf("<F> " str, ##__VA_ARGS__); }while(0)
#define logwohf(str,  ...) do{ os_printf(str, ##__VA_ARGS__); }while(0)
#else
#define logf(str,  ...) {}
#define logwohf(str,  ...) {}
#endif

#endif
