Tinkerforge/wifi-v2-extension/software/src/base64_encode.c

/*
 * This code originally came from here
 *
 * http://base64.sourceforge.net/b64.c
 *
 * with the following license:
 *
 * LICENCE:        Copyright (c) 2001 Bob Trower, Trantor Standard Systems Inc.
 *
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
 *                THE SOFTWARE IS PROVIDED "AS IS", WITHOUT WARRANTY OF ANY
 *                KIND, EXPRESS OR IMPLIED, INCLUDING BUT NOT LIMITED TO THE
 *                WARRANTIES OF MERCHANTABILITY, FITNESS FOR A PARTICULAR
 *                PURPOSE AND NONINFRINGEMENT. IN NO EVENT SHALL THE AUTHORS
 *                OR COPYRIGHT HOLDERS BE LIABLE FOR ANY CLAIM, DAMAGES OR
 *                OTHER LIABILITY, WHETHER IN AN ACTION OF CONTRACT, TORT OR
 *                OTHERWISE, ARISING FROM, OUT OF OR IN CONNECTION WITH THE
 *                SOFTWARE OR THE USE OR OTHER DEALINGS IN THE SOFTWARE.
 */

#include "base64_encode.h"

static const char encode[] = "ABCDEFGHIJKLMNOPQRSTUVWXYZ"
			     "abcdefghijklmnopqrstuvwxyz0123456789+/";

int32_t ICACHE_FLASH_ATTR base64_encode_string(const char *in, int32_t in_len, char *out, int32_t out_size) {
	unsigned char triple[3];
	int32_t i;
	int32_t len;
	int32_t line = 0;
	int32_t done = 0;

	while (in_len) {
		len = 0;
		for (i = 0; i < 3; i++) {
			if (in_len) {
				triple[i] = *in++;
				len++;
				in_len--;
			} else
				triple[i] = 0;
		}
		if (!len)
			continue;

		if (done + 4 >= out_size)
			return -1;

		*out++ = encode[triple[0] >> 2];
		*out++ = encode[((triple[0] & 0x03) << 4) |
					     ((triple[1] & 0xf0) >> 4)];
		*out++ = (len > 1 ? encode[((triple[1] & 0x0f) << 2) |
					     ((triple[2] & 0xc0) >> 6)] : '=');
		*out++ = (len > 2 ? encode[triple[2] & 0x3f] : '=');

		done += 4;
		line += 4;
	}

	if (done + 1 >= out_size)
		return -1;

	*out++ = '\0';

	return done;
}
